will07c5/eurorack/AS3360_VCA/AS3360_VCA.kicad_pcb

## KiCad design AS3360_VCA/AS3360_VCA.kicad_pcb (2019-09-10)

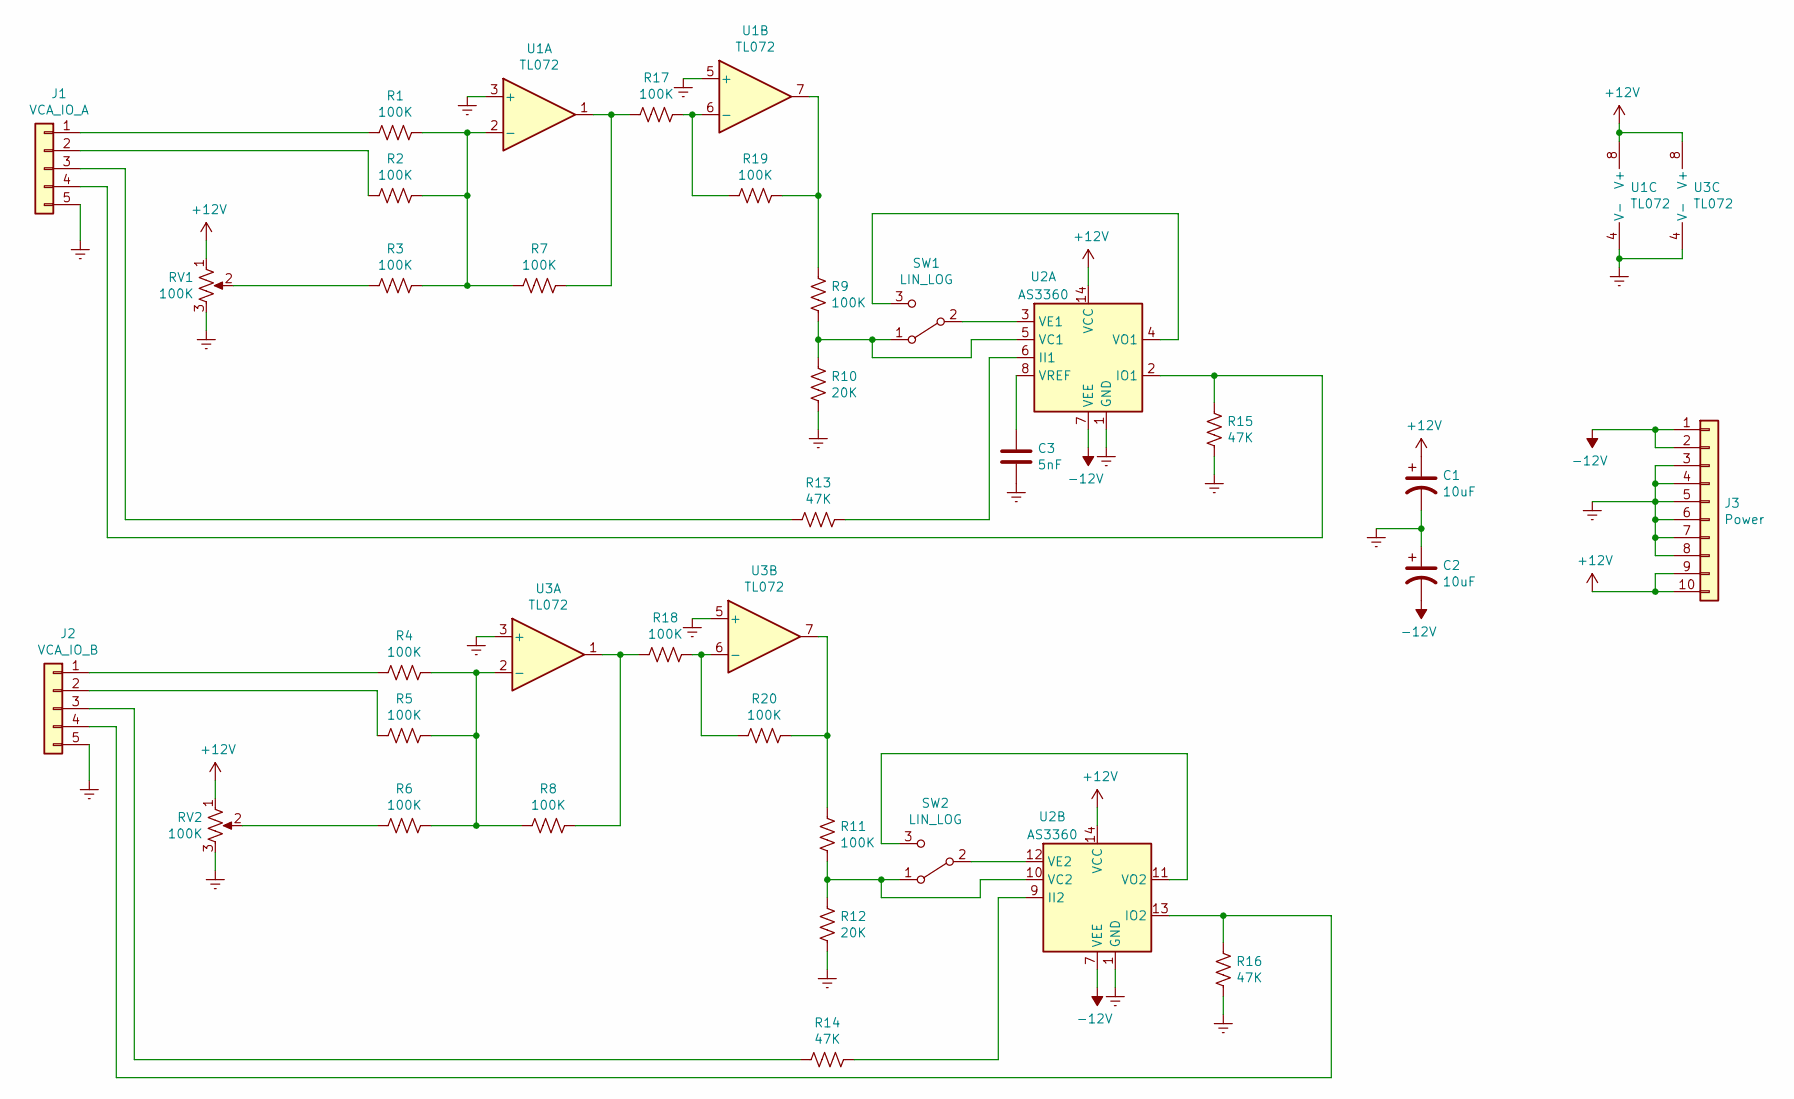
[picture p24: schematic AS3360_VCA.sch]

Parts:
C1, C2: 10uF; CP_Elec_4x3
C3: 5nF; C_0805_2012Metric
J1: VCA_IO_A; PinSocket_1x05_P2.54mm_Vertical
J2: VCA_IO_B; PinSocket_1x05_P2.54mm_Vertical
J3: Power; IDC-Header_2x05_P2.54mm_Vertical
R1, R2, R3, R4, R5, R6, R7, R8, R9, R11, R17, R18, R19, R20: 100K; R_0805_2012Metric
R10, R12: 20K; R_0805_2012Metric
R13, R14, R15, R16: 47K; R_0805_2012Metric
RV1, RV2: 100K; PinSocket_1x03_P2.54mm_Vertical
SW1, SW2: LIN_LOG; PinSocket_1x03_P2.54mm_Vertical
U1, U3: TL072; DIP-8_W7.62mm
U2: AS3360; DIP-14_W7.62mm

Connections:
+12V: C1.1, J3.9, J3.10, RV1.1, RV2.1, U1.8 (V+), U2.14 (VCC), U3.8 (V+)
-12V: C2.2, J3.1, J3.2, U2.7 (VEE)
GNDREF: C1.2, C2.1, C3.2, J1.5, J2.5, J3.3, J3.4, J3.5, J3.6, J3.7, J3.8, R10.2, R12.2, R15.2, R16.2, RV1.3, RV2.3, U1.3 (+), U1.4 (V-), U1.5 (+), U2.1 (GND), U3.3 (+), U3.4 (V-), U3.5 (+)
unnamed: C3.1, U2.8 (VREF)
unnamed: J1.1, R1.2
unnamed: J1.2, R2.2
unnamed: J1.3, R13.2
unnamed: J1.4, R15.1, U2.2 (IO1)
unnamed: J2.1, R4.2
unnamed: J2.2, R5.2
unnamed: J2.3, R14.2
unnamed: J2.4, R16.1, U2.13 (IO2)
unnamed: R1.1, R2.1, R3.1, R7.2, U1.2 (-)
unnamed: R3.2, RV1.2
unnamed: R4.1, R5.1, R6.1, R8.2, U3.2 (-)
unnamed: R6.2, RV2.2
unnamed: R9.2, R10.1, SW1.1 (A), U2.5 (VC1)
unnamed: R11.1, R20.1, U3.7
unnamed: R11.2, R12.1, SW2.1 (A), U2.10 (VC2)
unnamed: R13.1, U2.6 (II1)
unnamed: R14.1, U2.9 (II2)
unnamed: R17.1, R19.2, U1.6 (-)
unnamed: R7.1, R17.2, U1.1
unnamed: R18.1, R20.2, U3.6 (-)
unnamed: R8.1, R18.2, U3.1
unnamed: R9.1, R19.1, U1.7
unnamed: SW1.2 (B), U2.3 (VE1)
unnamed: SW1.3 (C), U2.4 (VO1)
unnamed: SW2.2 (B), U2.12 (VE2)
unnamed: SW2.3 (C), U2.11 (VO2)

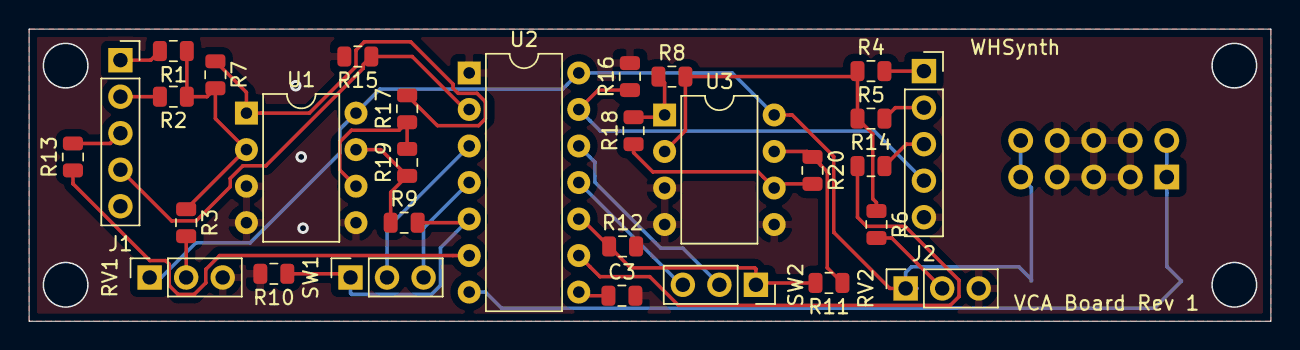
[picture p25: board AS3360_VCA.kicad_pcb from above]

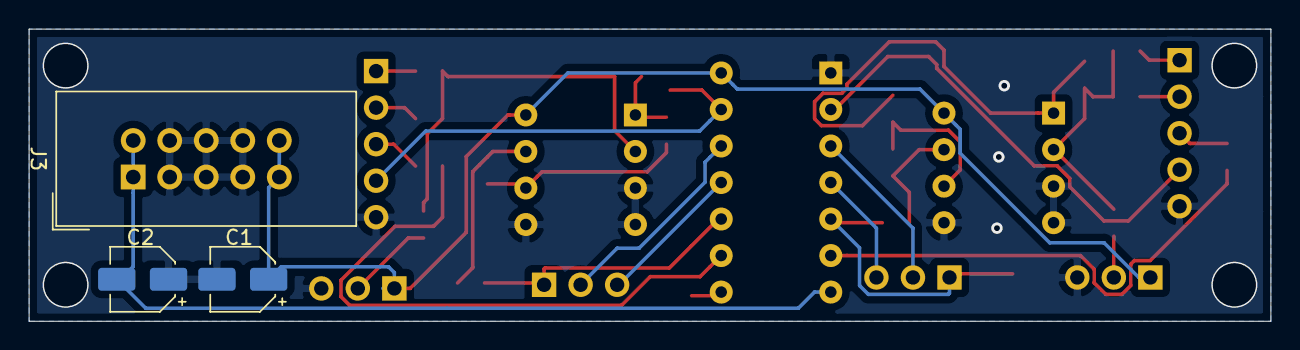
[picture p26: board AS3360_VCA.kicad_pcb from below]

Board: 2 copper layers, 86.4 x 20.3 mm, 33 parts (3 on the bottom side), 30 nets.
